MOSH-Insa-Toulouse/Francois-Pierre-Project/Images/Code_APK.PNG

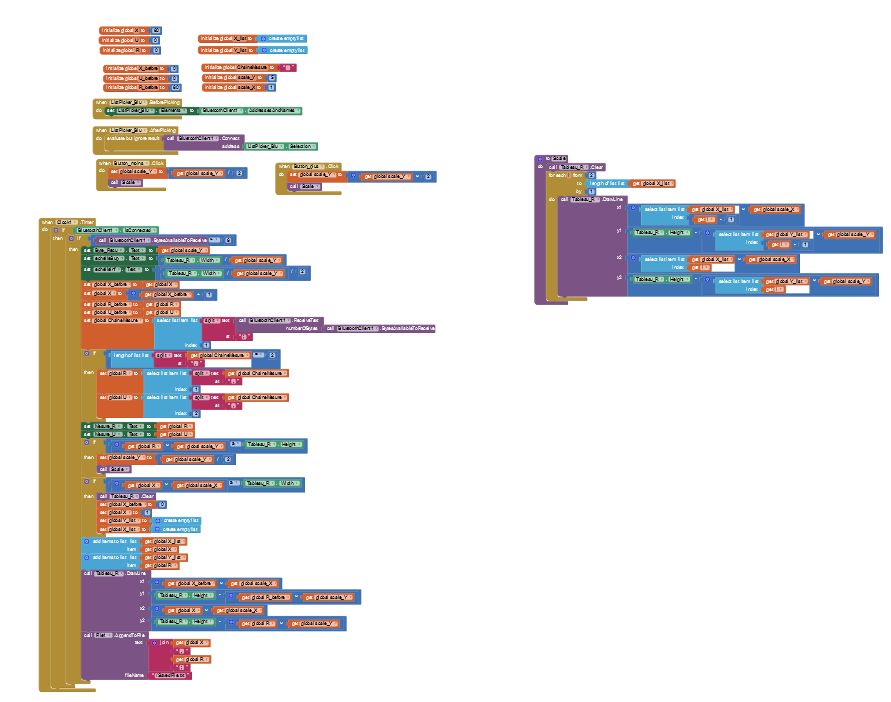
Images/Code_APK.PNG
