MOSH-Insa-Toulouse/Francois-Pierre-Project/Images/Routage_sans_compo.PNG

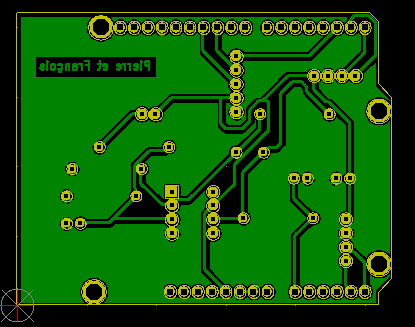
Images/Routage_sans_compo.PNG
